CedarGroveStudios/NAU7802_24-bit_ADC_FeatherWing/graphics/Clue_Scale_dual_2021-01-10.jpeg

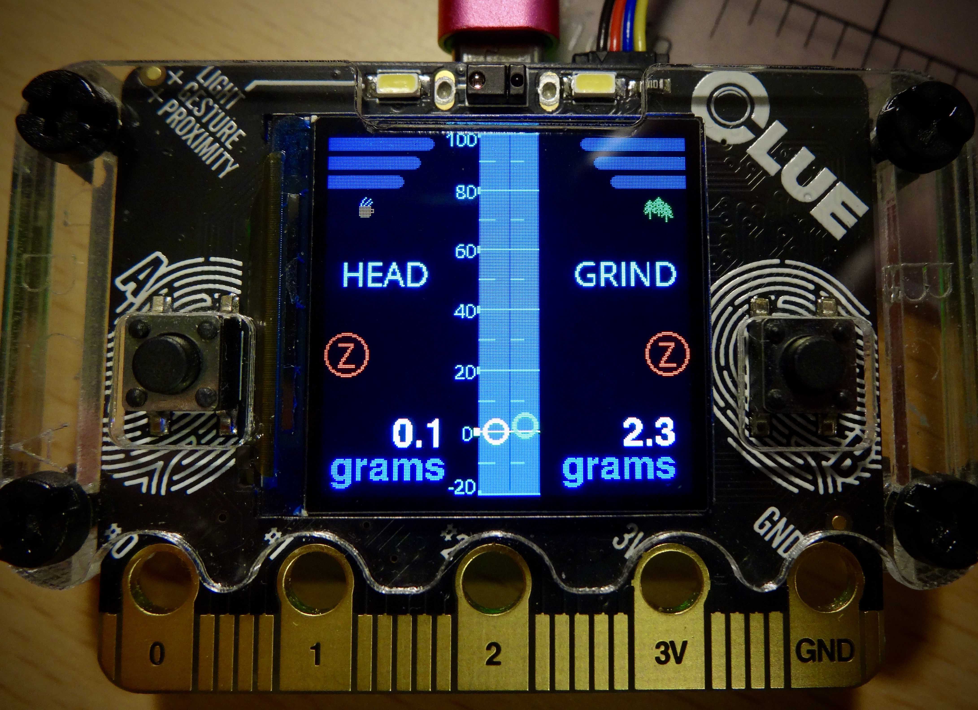
graphics/Clue_Scale_dual_2021-01-10.jpeg
