CedarGroveStudios/NAU7802_24-bit_ADC_FeatherWing/graphics/NAU7802_Dual_24-bit_ADC_anno_1.png

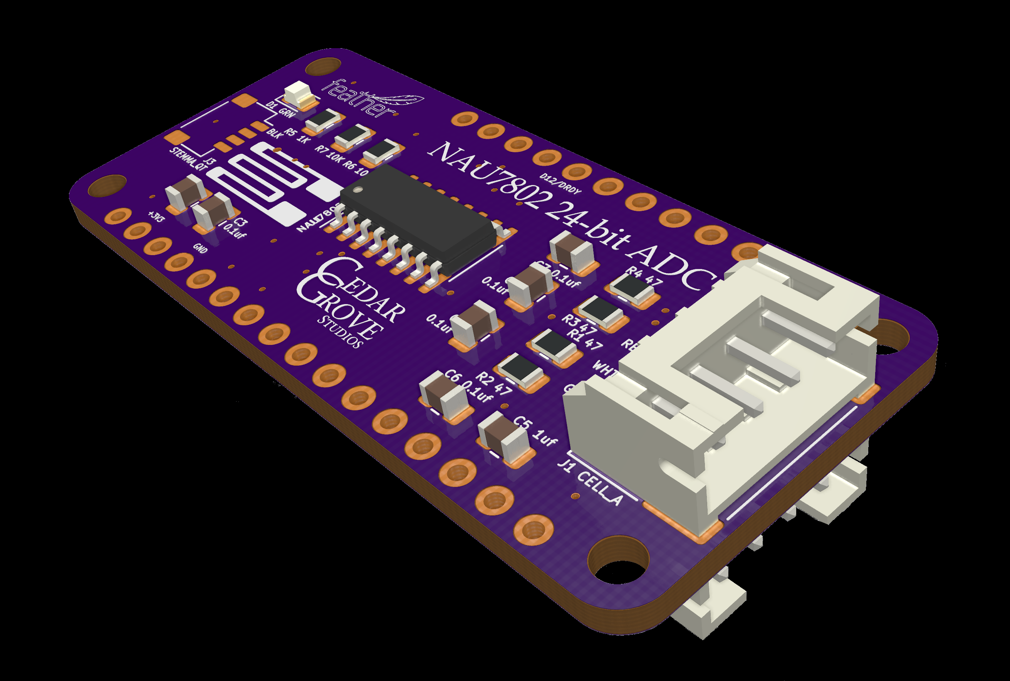
graphics/NAU7802_Dual_24-bit_ADC_anno_1.png
