CedarGroveStudios/NAU7802_24-bit_ADC_FeatherWing/graphics/NAU7802_social.png

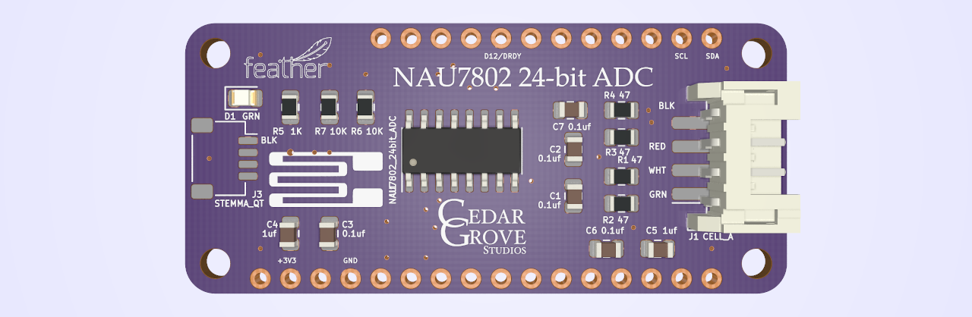
graphics/NAU7802_social.png
