CedarGroveStudios/NAU7802_24-bit_ADC_FeatherWing/graphics/strain_gauge_sample_image.png

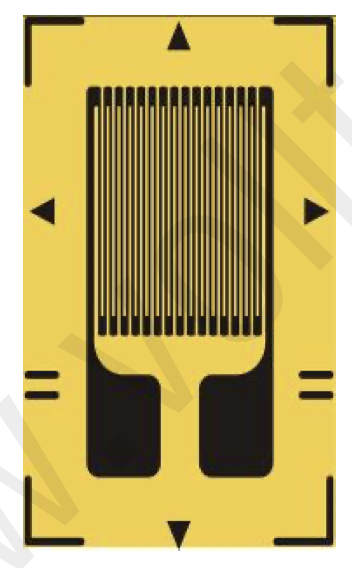
graphics/strain_gauge_sample_image.png
