CedarGroveStudios/NAU7802_24-bit_ADC_FeatherWing/pcb/pcb_top_copper.png

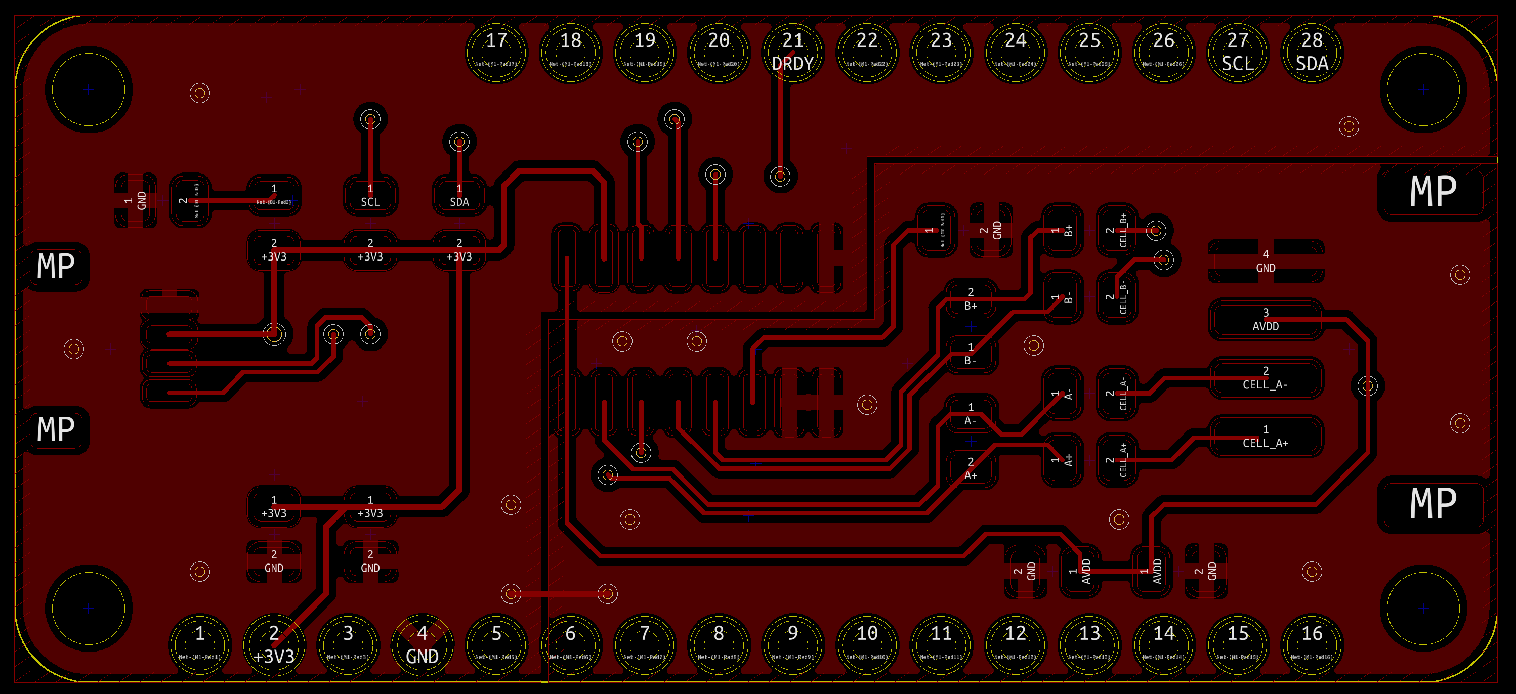
pcb/pcb_top_copper.png
