CedarGroveStudios/NAU7802_24-bit_ADC_FeatherWing/pcb_DIP/NAU7802_Dual_24-bit_ADC_DIP.png

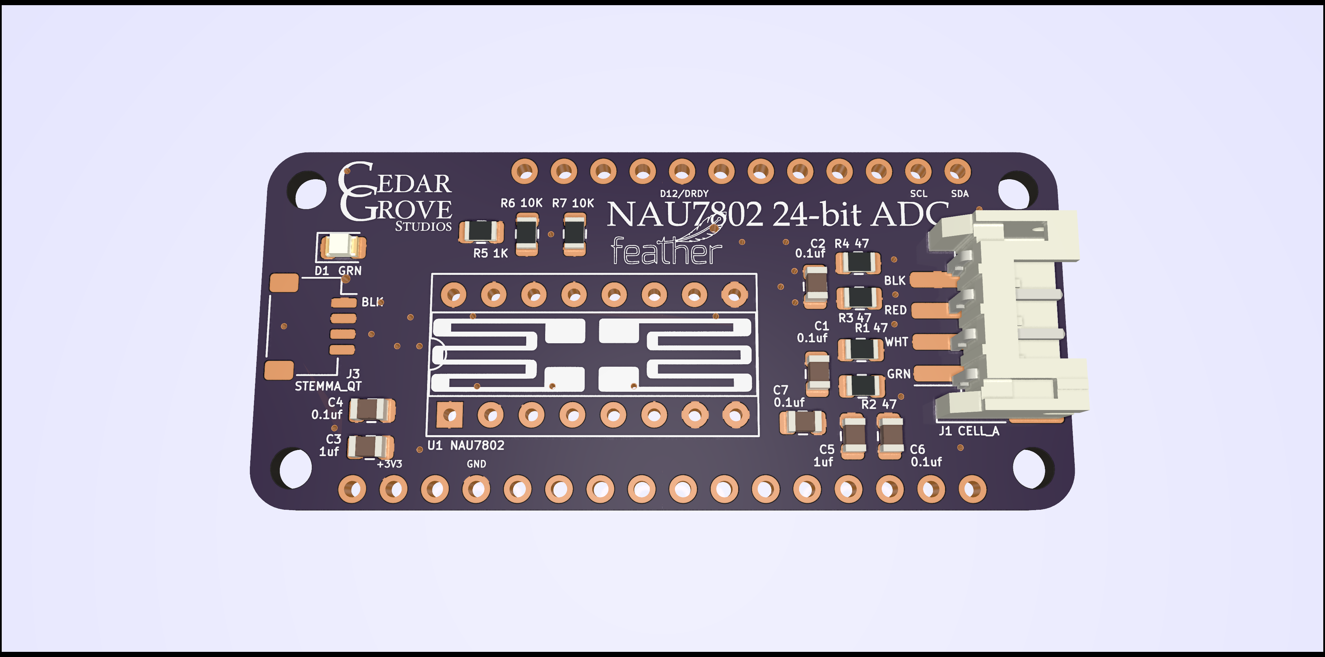
pcb_DIP/NAU7802_Dual_24-bit_ADC_DIP.png
