CedarGroveStudios/NAU7802_24-bit_ADC_FeatherWing/graphics/NAU7802_load_cell_wiring.jpeg

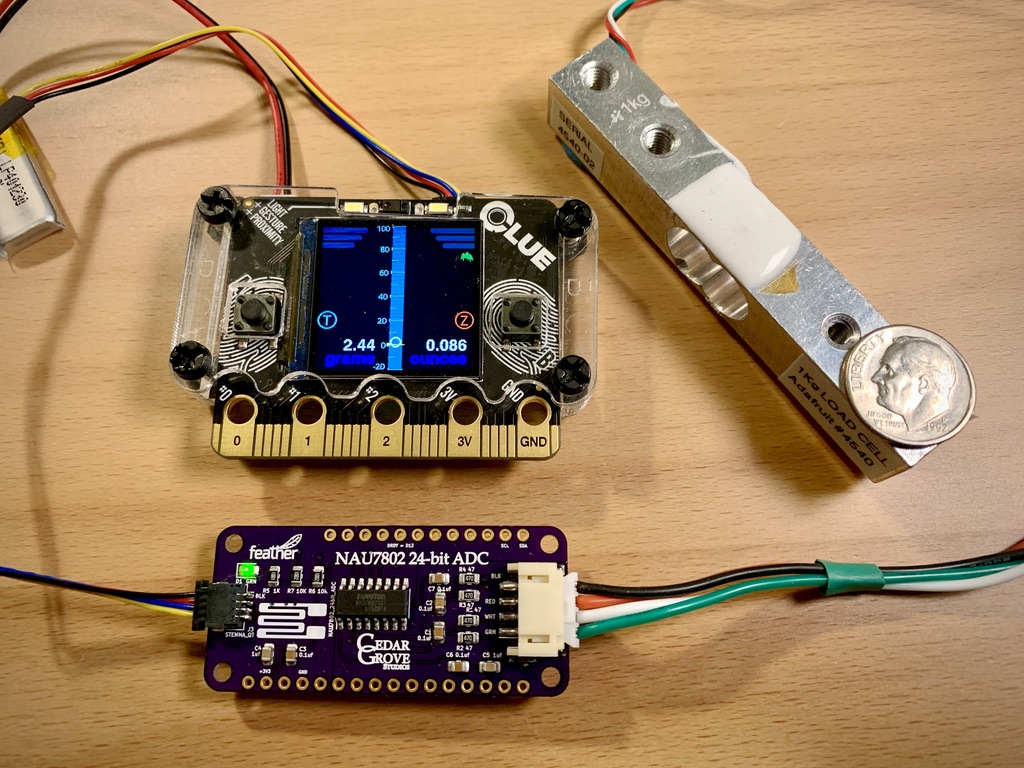
graphics/NAU7802_load_cell_wiring.jpeg
