CedarGroveStudios/NAU7802_24-bit_ADC_FeatherWing/graphics/nau7802_analog_mux_settle_test_2021-01-10.png

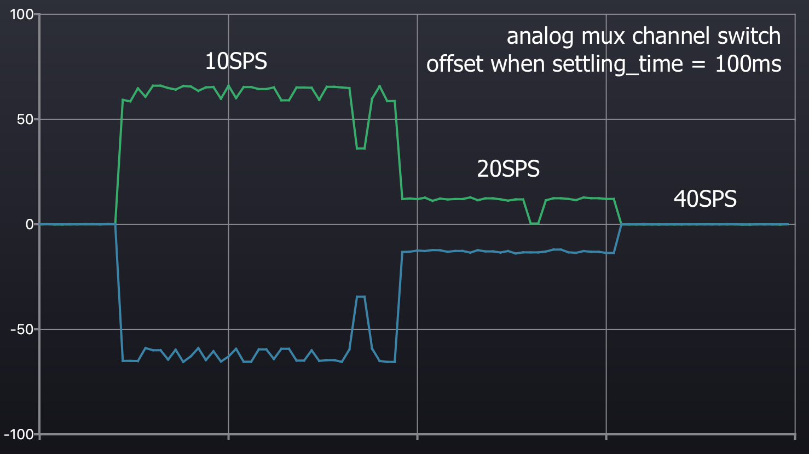
graphics/nau7802_analog_mux_settle_test_2021-01-10.png
